Frank-08/zmk-config/dad-no-arrows/stl/dad-no-arrows_section_1_top.stl

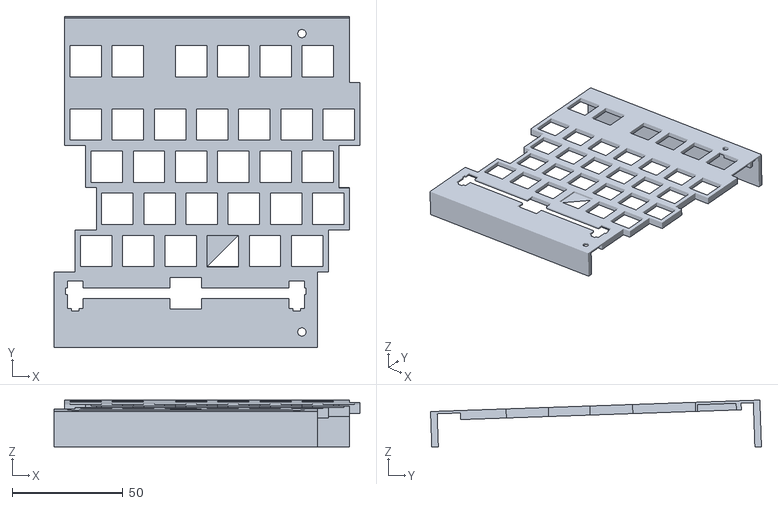
[picture p24: CAD file, 2025-01-27]
dad-no-arrows/stl/dad-no-arrows_section_1_top.stl
138.1 x 149.5 x 21.2
