Frank-08/zmk-config/dad-no-arrows/stl/dad-no-arrows_section_2_plate.stl

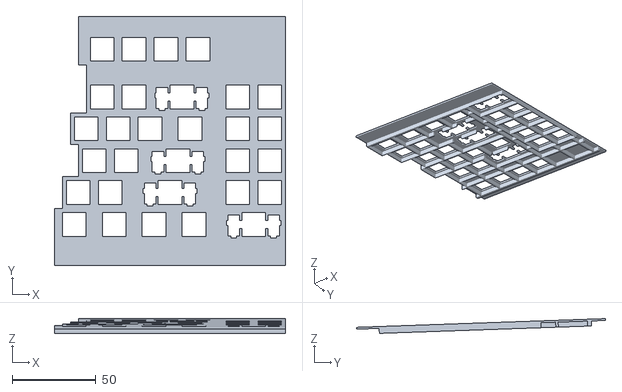
[picture p25: CAD file, 2025-01-27]
dad-no-arrows/stl/dad-no-arrows_section_2_plate.stl
138.1 x 148.8 x 8.83
