Frank-08/zmk-config/dad-no-arrows/stl/dad-no-arrows_section_1_all.stl

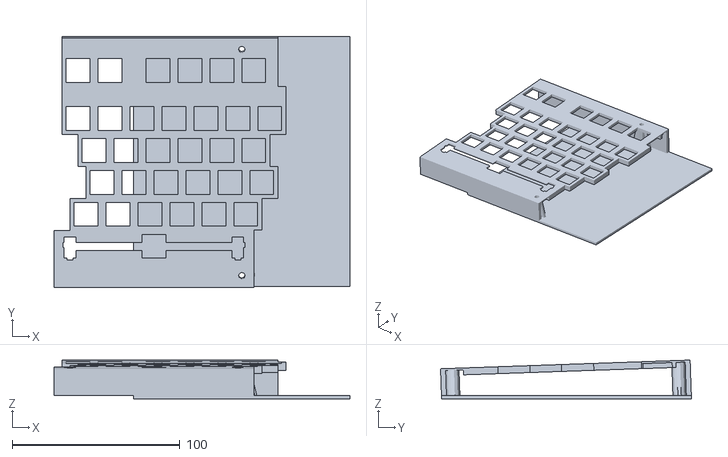
[picture p26: CAD file, 2025-01-27]
dad-no-arrows/stl/dad-no-arrows_section_1_all.stl
176.4 x 149.5 x 23.2
