Frank-08/zmk-config/dad-no-arrows/stl/dad-no-arrows_section_0_plate.stl

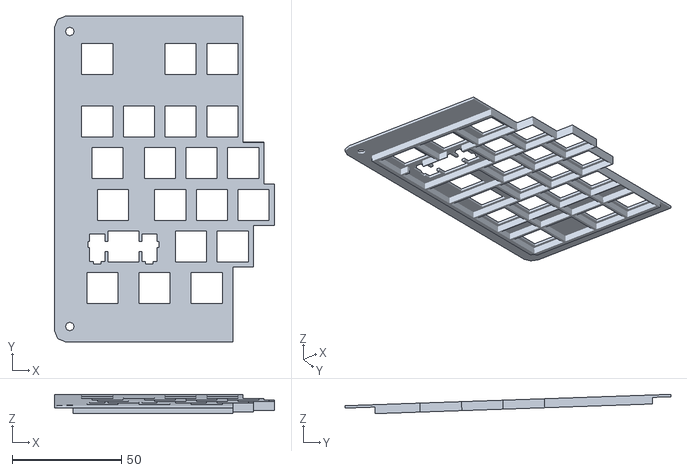
[picture p27: CAD file, 2025-01-27]
dad-no-arrows/stl/dad-no-arrows_section_0_plate.stl
100.5 x 148.8 x 8.83
